nk-kotsomitis/iot-system-agriculture/environment_sensor/SHT40/sensirion_common.h

/*
 * Copyright (c) 2018, Sensirion AG
 * All rights reserved.
 *
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
 * * Neither the name of Sensirion AG nor the names of its
 *   contributors may be used to endorse or promote products derived from
 *   this software without specific prior written permission.
 *
 * THIS SOFTWARE IS PROVIDED BY THE COPYRIGHT HOLDERS AND CONTRIBUTORS "AS IS"
 * AND ANY EXPRESS OR IMPLIED WARRANTIES, INCLUDING, BUT NOT LIMITED TO, THE
 * IMPLIED WARRANTIES OF MERCHANTABILITY AND FITNESS FOR A PARTICULAR PURPOSE
 * ARE DISCLAIMED. IN NO EVENT SHALL THE COPYRIGHT HOLDER OR CONTRIBUTORS BE
 * LIABLE FOR ANY DIRECT, INDIRECT, INCIDENTAL, SPECIAL, EXEMPLARY, OR
 * CONSEQUENTIAL DAMAGES (INCLUDING, BUT NOT LIMITED TO, PROCUREMENT OF
 * SUBSTITUTE GOODS OR SERVICES; LOSS OF USE, DATA, OR PROFITS; OR BUSINESS
 * INTERRUPTION) HOWEVER CAUSED AND ON ANY THEORY OF LIABILITY, WHETHER IN
 * CONTRACT, STRICT LIABILITY, OR TORT (INCLUDING NEGLIGENCE OR OTHERWISE)
 * ARISING IN ANY WAY OUT OF THE USE OF THIS SOFTWARE, EVEN IF ADVISED OF THE
 * POSSIBILITY OF SUCH DAMAGE.
 */

#ifndef SENSIRION_COMMON_H
#define SENSIRION_COMMON_H

#include "sensirion_arch_config.h"

#ifdef __cplusplus
extern "C" {
#endif

#define NO_ERROR 0
#define ERROR_I2C_READ_START 1
#define ERROR_I2C_READ_MIN_BYTES 2
#define ERROR_I2C_WRITE_START 3
#define ERROR_I2C_WRITE 4

/* deprecated defines, use NO_ERROR or custom error codes instead */
#define STATUS_OK 0
#define STATUS_FAIL (-1)

#ifndef ARRAY_SIZE
#define ARRAY_SIZE(x) (sizeof(x) / sizeof(*(x)))
#endif

#define CRC8_POLYNOMIAL 0x31
#define CRC8_INIT 0xFF
#define CRC8_LEN 1

#define SENSIRION_COMMAND_SIZE 2
#define SENSIRION_WORD_SIZE 2
#define SENSIRION_NUM_WORDS(x) (sizeof(x) / SENSIRION_WORD_SIZE)
#define SENSIRION_MAX_BUFFER_WORDS 32

/**
 * sensirion_bytes_to_uint16_t() - Convert an array of bytes to an uint16_t
 *
 * Convert an array of bytes received from the sensor in big-endian/MSB-first
 * format to an uint16_t value in the correct system-endianness.
 *
 * @param bytes An array of at least two bytes (MSB first)
 * @return      The byte array represented as uint16_t
 */
uint16_t sensirion_bytes_to_uint16_t(const uint8_t* bytes);

/**
 * sensirion_bytes_to_uint32_t() - Convert an array of bytes to an uint32_t
 *
 * Convert an array of bytes received from the sensor in big-endian/MSB-first
 * format to an uint32_t value in the correct system-endianness.
 *
 * @param bytes An array of at least four bytes (MSB first)
 * @return      The byte array represented as uint32_t
 */
uint32_t sensirion_bytes_to_uint32_t(const uint8_t* bytes);

/**
 * sensirion_bytes_to_float() - Convert an array of bytes to a float
 *
 * Convert an array of bytes received from the sensor in big-endian/MSB-first
 * format to an float value in the correct system-endianness.
 *
 * @param bytes An array of at least four bytes (MSB first)
 * @return      The byte array represented as float
 */
float sensirion_bytes_to_float(const uint8_t* bytes);

uint8_t sensirion_common_generate_crc(const uint8_t* data, uint16_t count);

int8_t sensirion_common_check_crc(const uint8_t* data, uint16_t count,
                                  uint8_t checksum);

/**
 * sensirion_i2c_general_call_reset() - Send a general call reset.
 *
 * @warning This will reset all attached I2C devices on the bus which support
 *          general call reset.
 *
 * @return  NO_ERROR on success, an error code otherwise
 */
int16_t sensirion_i2c_general_call_reset(void);

/**
 * sensirion_fill_cmd_send_buf() - create the i2c send buffer for a command and
 *                                 a set of argument words. The output buffer
 *                                 interleaves argument words with their
 *                                 checksums.
 * @buf:        The generated buffer to send over i2c. Then buffer length must
 *              be at least SENSIRION_COMMAND_LEN + num_args *
 *              (SENSIRION_WORD_SIZE + CRC8_LEN).
 * @cmd:        The i2c command to send. It already includes a checksum.
 * @args:       The arguments to the command. Can be NULL if none.
 * @num_args:   The number of word arguments in args.
 *
 * @return      The number of bytes written to buf
 */
uint16_t sensirion_fill_cmd_send_buf(uint8_t* buf, uint16_t cmd,
                                     const uint16_t* args, uint8_t num_args);

/**
 * sensirion_i2c_read_words() - read data words from sensor
 *
 * @address:    Sensor i2c address
 * @data_words: Allocated buffer to store the read words.
 *              The buffer may also have been modified on STATUS_FAIL return.
 * @num_words:  Number of data words to read (without CRC bytes)
 *
 * @return      NO_ERROR on success, an error code otherwise
 */
int16_t sensirion_i2c_read_words(uint8_t address, uint16_t* data_words,
                                 uint16_t num_words);

/**
 * sensirion_i2c_read_words_as_bytes() - read data words as byte-stream from
 *                                       sensor
 *
 * Read bytes without adjusting values to the uP's word-order.
 *
 * @address:    Sensor i2c address
 * @data:       Allocated buffer to store the read bytes.
 *              The buffer may also have been modified on STATUS_FAIL return.
 * @num_words:  Number of data words(!) to read (without CRC bytes)
 *              Since only word-chunks can be read from the sensor the size
 *              is still specified in sensor-words (num_words = num_bytes *
 *              SENSIRION_WORD_SIZE)
 *
 * @return      NO_ERROR on success, an error code otherwise
 */
int16_t sensirion_i2c_read_words_as_bytes(uint8_t address, uint8_t* data,
                                          uint16_t num_words);

/**
 * sensirion_i2c_write_cmd() - writes a command to the sensor
 * @address:    Sensor i2c address
 * @command:    Sensor command
 *
 * @return      NO_ERROR on success, an error code otherwise
 */
int16_t sensirion_i2c_write_cmd(uint8_t address, uint16_t command);

/**
 * sensirion_i2c_write_cmd_with_args() - writes a command with arguments to the
 *                                       sensor
 * @address:    Sensor i2c address
 * @command:    Sensor command
 * @data:       Argument buffer with words to send
 * @num_words:  Number of data words to send (without CRC bytes)
 *
 * @return      NO_ERROR on success, an error code otherwise
 */
int16_t sensirion_i2c_write_cmd_with_args(uint8_t address, uint16_t command,
                                          const uint16_t* data_words,
                                          uint16_t num_words);

/**
 * sensirion_i2c_delayed_read_cmd() - send a command, wait for the sensor to
 *                                    process and read data back
 * @address:    Sensor i2c address
 * @cmd:        Command
 * @delay:      Time in microseconds to delay sending the read request
 * @data_words: Allocated buffer to store the read data
 * @num_words:  Data words to read (without CRC bytes)
 *
 * @return      NO_ERROR on success, an error code otherwise
 */
int16_t sensirion_i2c_delayed_read_cmd(uint8_t address, uint16_t cmd,
                                       uint32_t delay_us, uint16_t* data_words,
                                       uint16_t num_words);
/**
 * sensirion_i2c_read_cmd() - reads data words from the sensor after a command
 *                            is issued
 * @address:    Sensor i2c address
 * @cmd:        Command
 * @data_words: Allocated buffer to store the read data
 * @num_words:  Data words to read (without CRC bytes)
 *
 * @return      NO_ERROR on success, an error code otherwise
 */
int16_t sensirion_i2c_read_cmd(uint8_t address, uint16_t cmd,
                               uint16_t* data_words, uint16_t num_words);

#ifdef __cplusplus
}
#endif

#endif /* SENSIRION_COMMON_H */
